sophiayduan/Endev-board/images/led strip/pcb.png

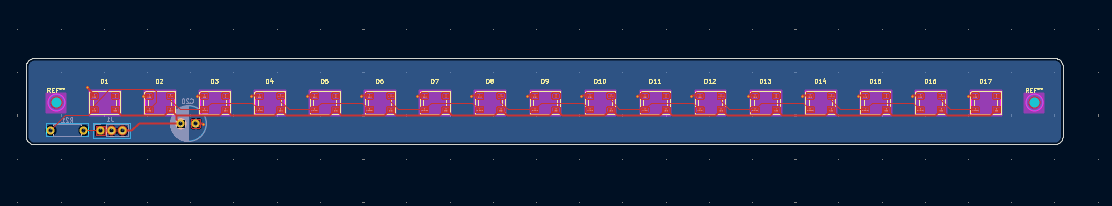
images/led strip/pcb.png
