sophiayduan/Endev-board/images/ledstrip.png

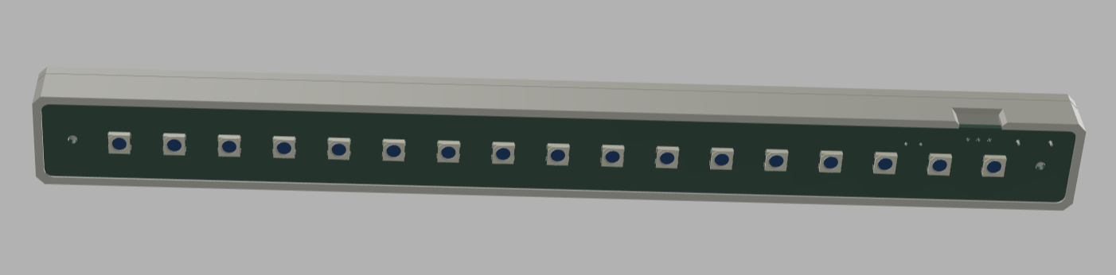
images/ledstrip.png
