sophiayduan/Endev-board/images/3d prints/back_encoder.png

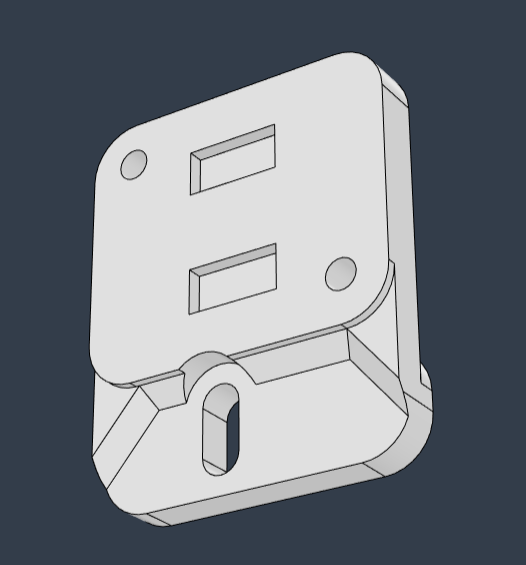
images/3d prints/back_encoder.png
