sophiayduan/Endev-board/images/3d prints/back_main.png

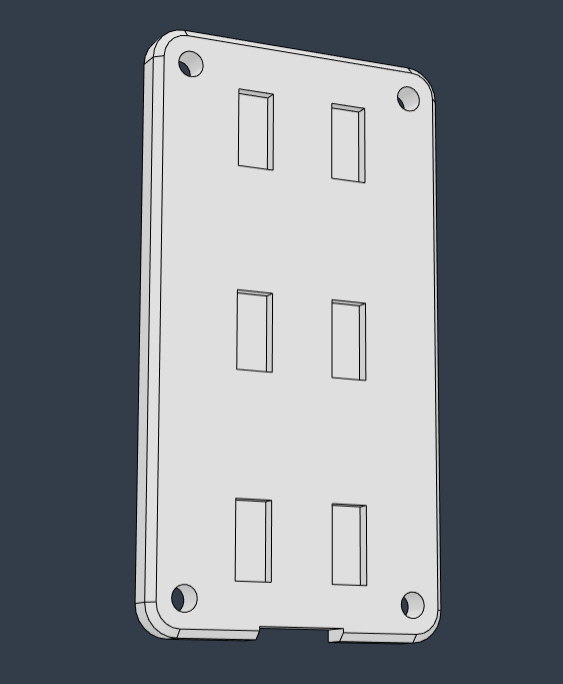
images/3d prints/back_main.png
