sophiayduan/Endev-board/images/3d prints/front_encoder.png

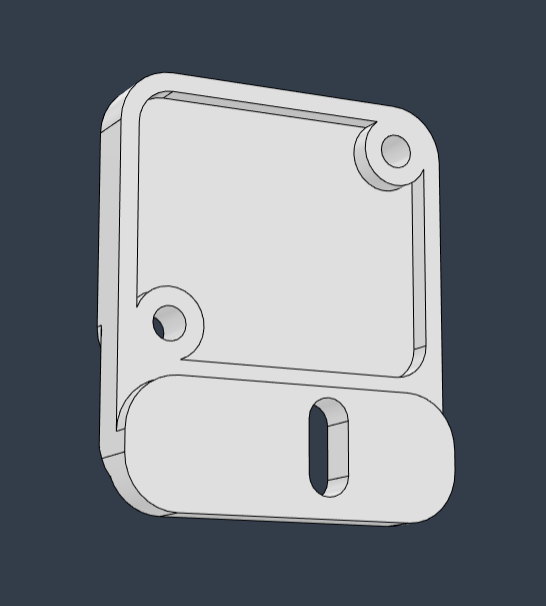
images/3d prints/front_encoder.png
