sophiayduan/Endev-board/images/3d prints/front_main.png

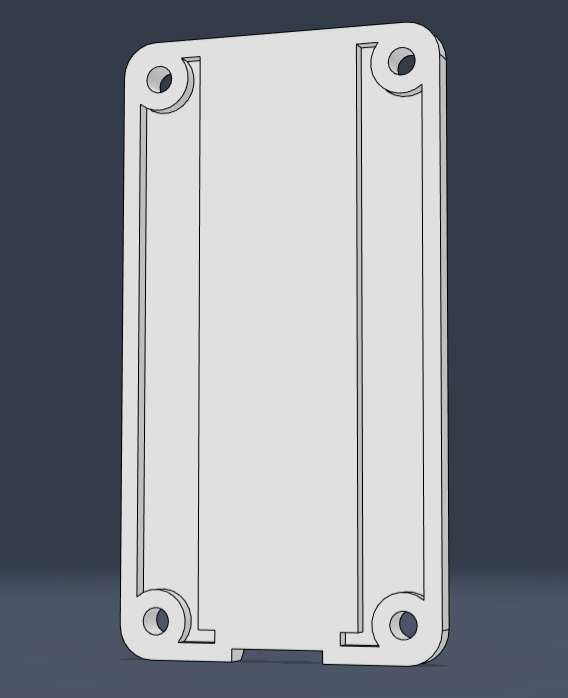
images/3d prints/front_main.png
