sophiayduan/Endev-board/images/3d prints/led_base.png

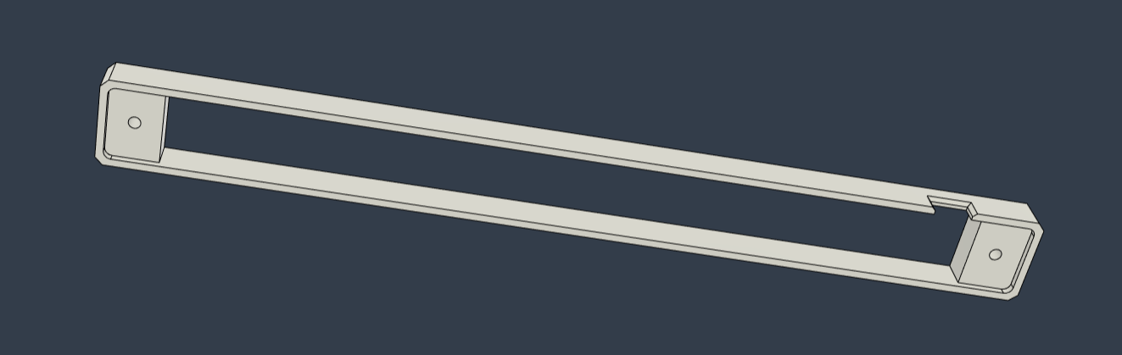
images/3d prints/led_base.png
