sophiayduan/Endev-board/images/3d prints/led_lid.png

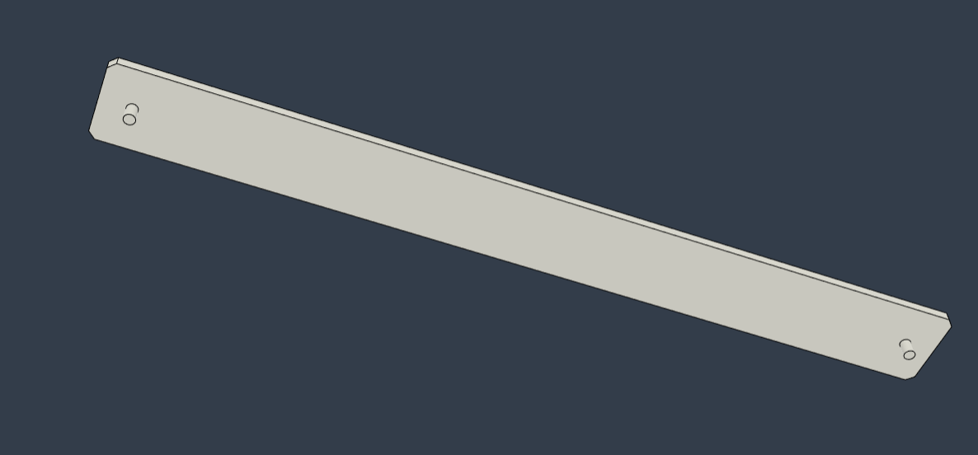
images/3d prints/led_lid.png
